RlinkSystem/SBC09-CPU_X-3_rev-3/CPU_X-3_Prints/OLD_v2/CPU_X-3_PCB_gray3.pdf

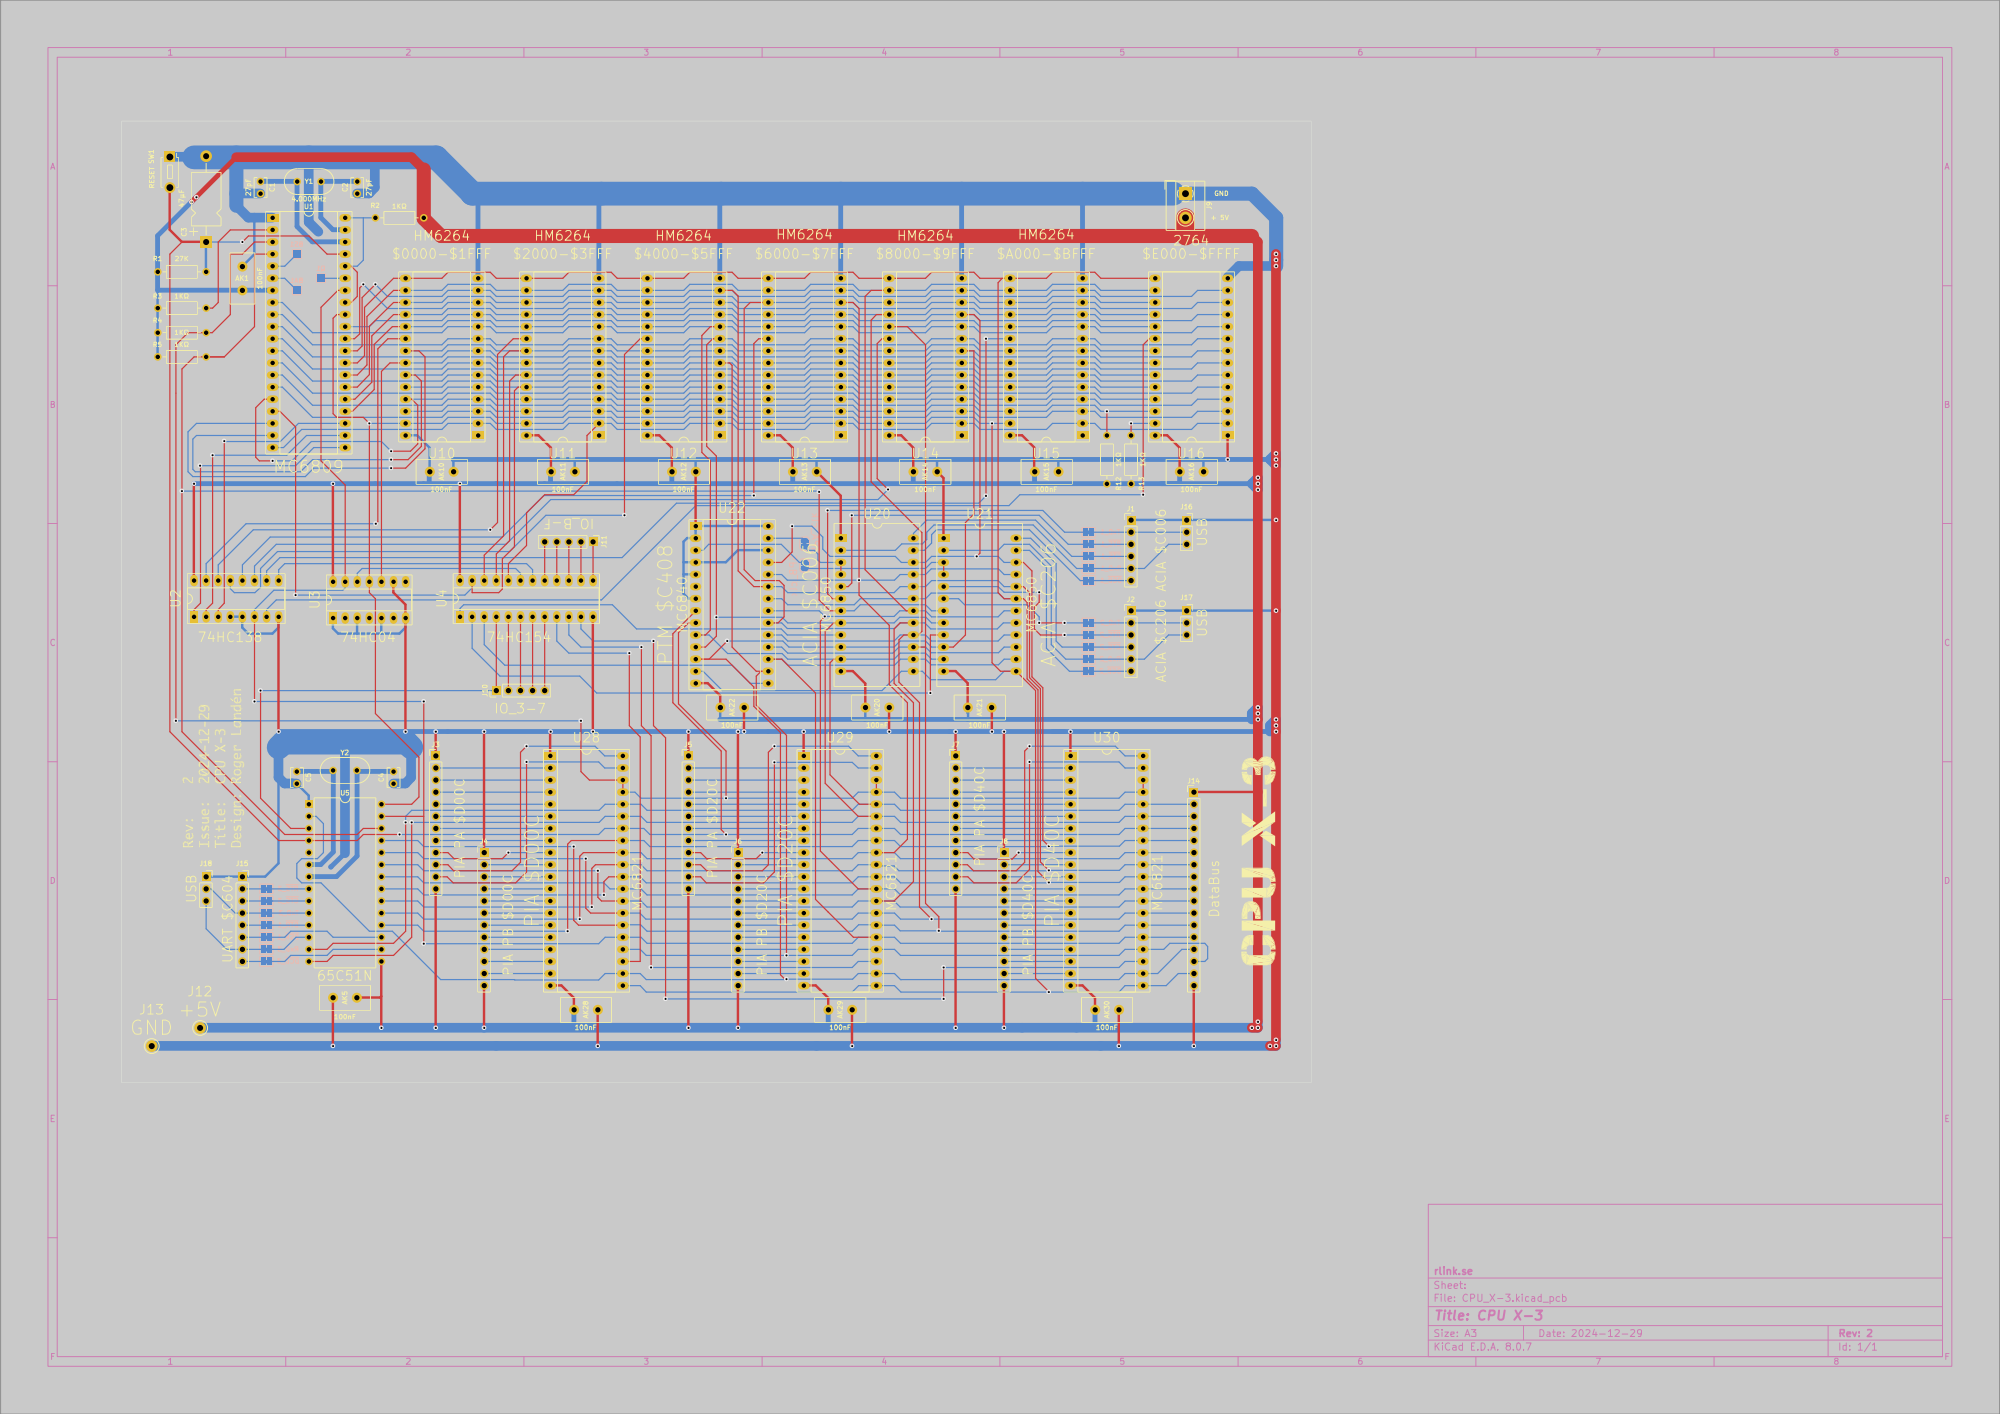
[picture p18: page 1]
