RlinkSystem/SBC09-CPU_X-3_rev-3/CPU_X-3_Prints/OLD_v2/CPU_X-3_PCB_max.pdf

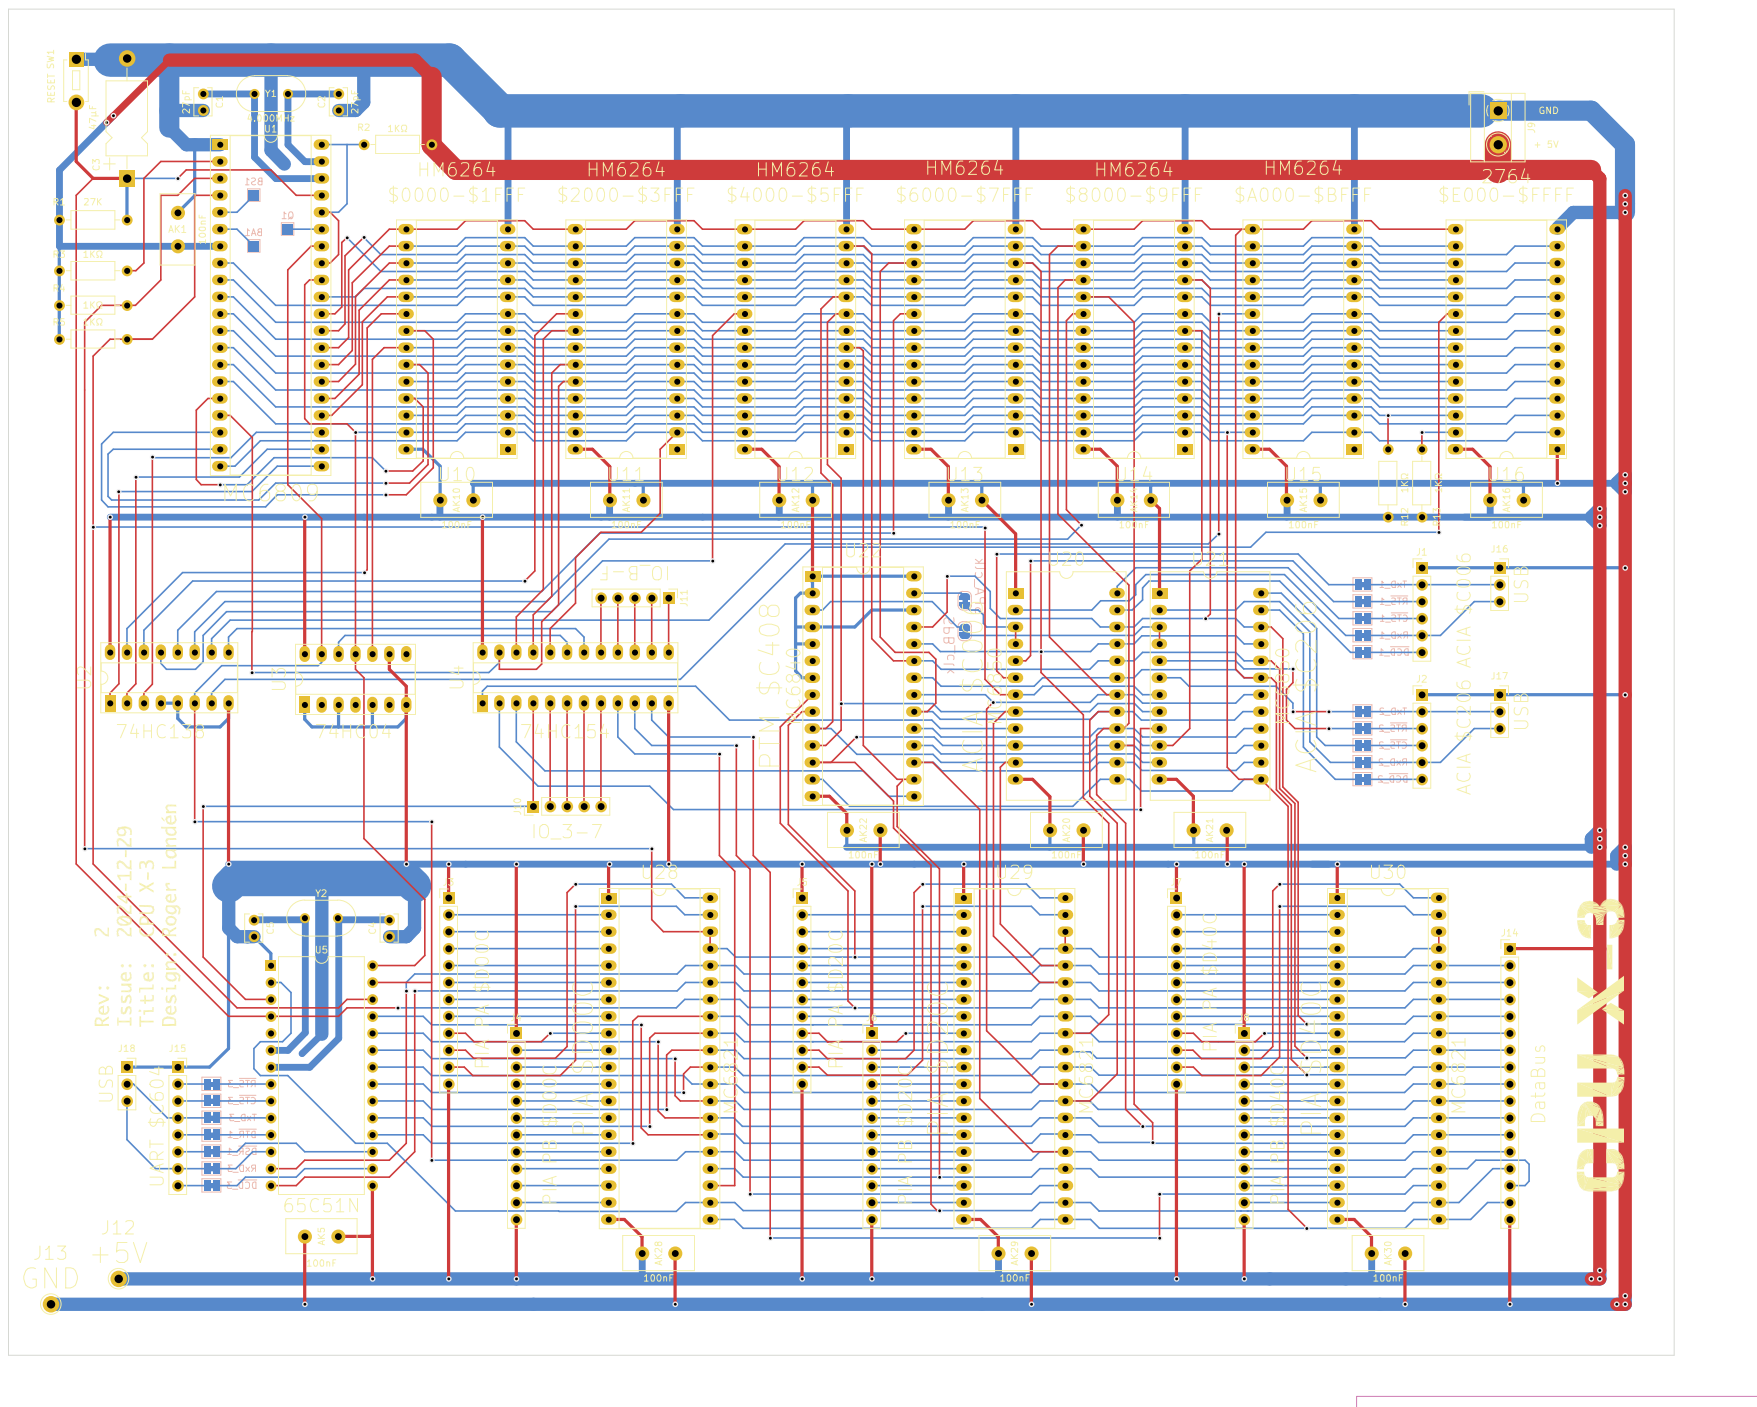
[picture p22: page 1]
