RlinkSystem/SBC09-CPU_X-3_rev-3/CPU_X-3_Prints/OLD_v2/CPU_x-3_Schematic.pdf

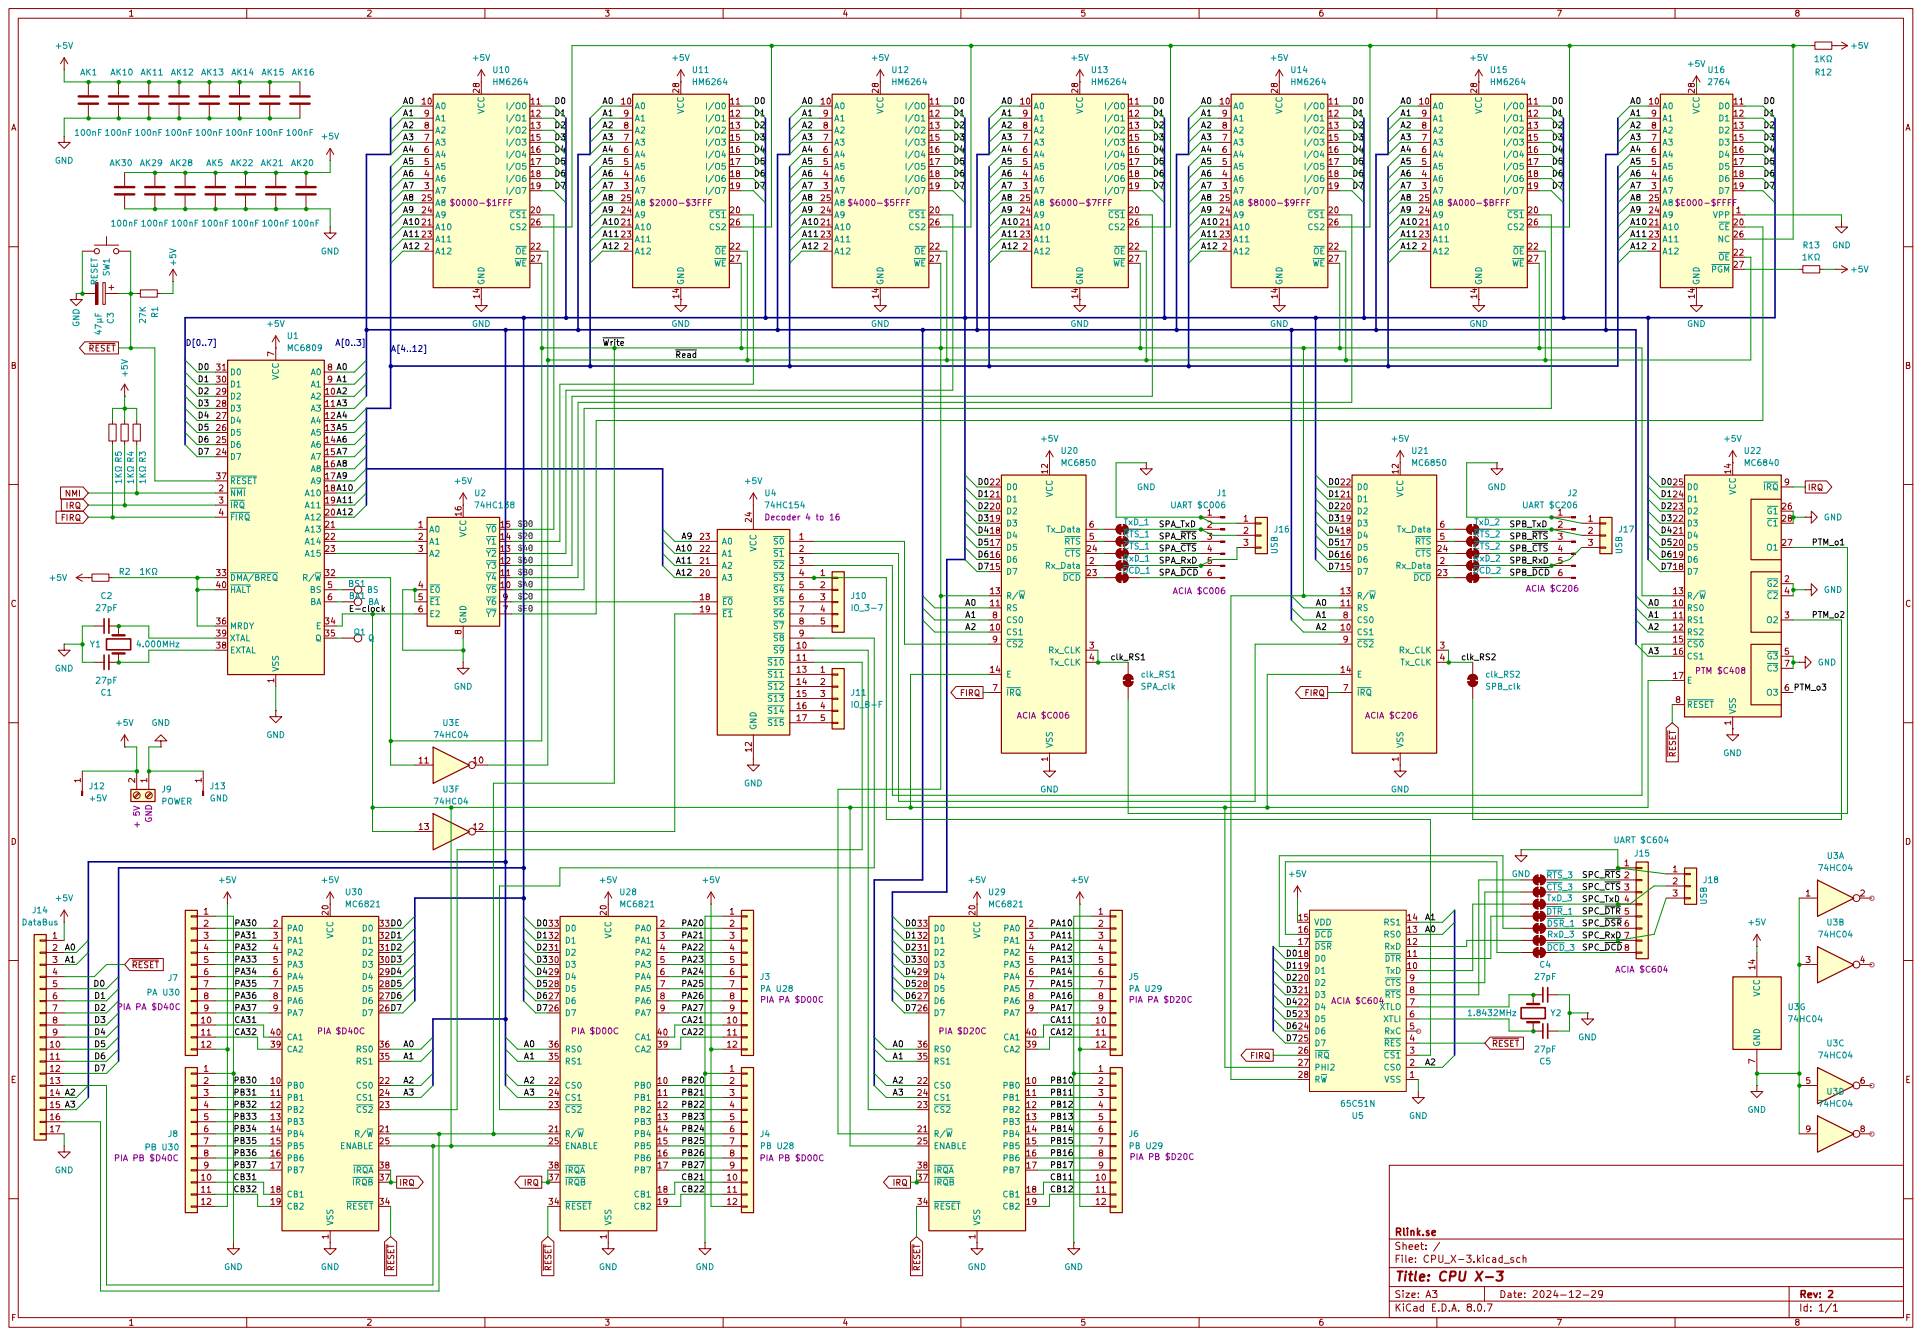
[picture p25: page 1]
